nickthelegend/cell-4b/out/stl/cartridge_null.stl

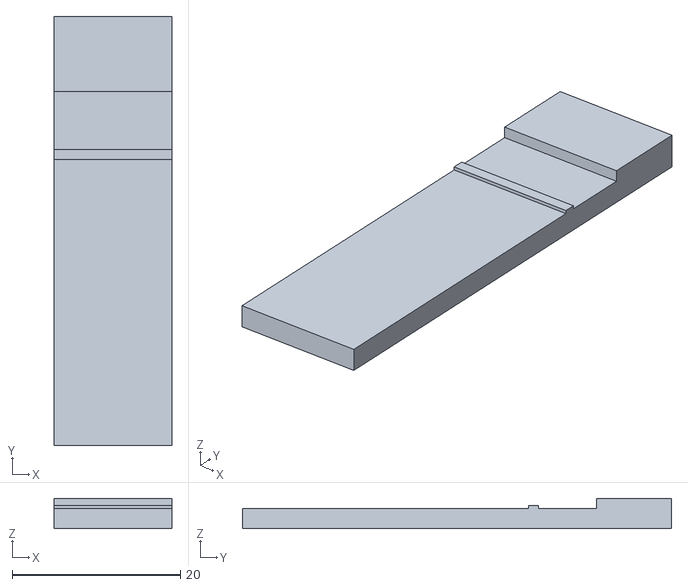
[picture p15: CAD file, 2026-08-31]
out/stl/cartridge_null.stl
14.0 x 51.0 x 3.60
