nickthelegend/cell-4b/out/stl/aperture_tube.stl

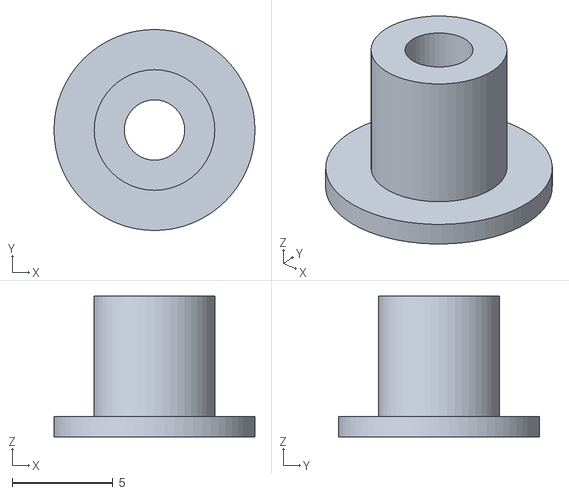
[picture p16: CAD file, 2026-08-31]
out/stl/aperture_tube.stl
10.0 x 10.0 x 7.00
