nickthelegend/cell-4b/out/stl/window_jig.stl

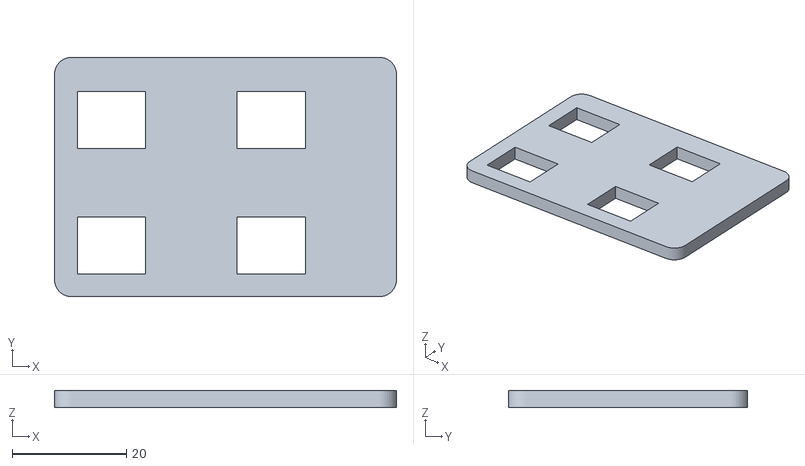
[picture p18: CAD file, 2026-08-31]
out/stl/window_jig.stl
60.0 x 42.0 x 3.00
