nickthelegend/cell-4b/out/stl/cartridge.stl

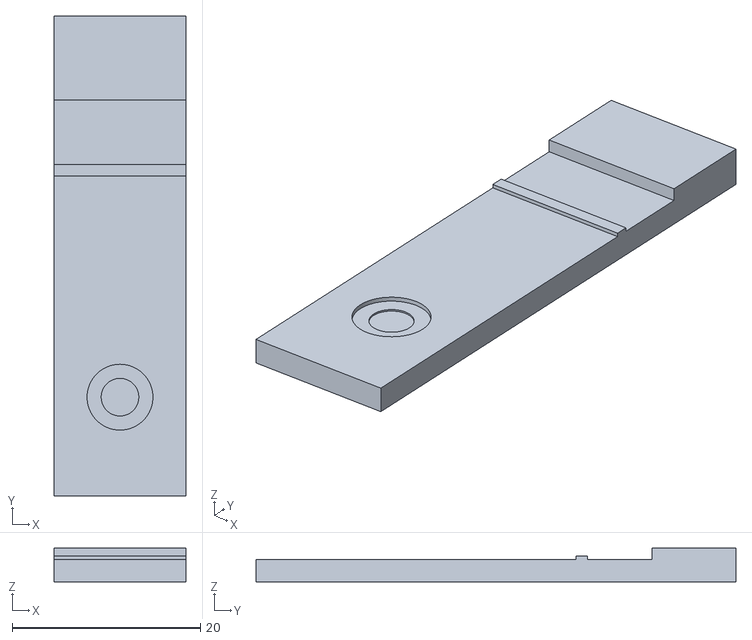
[picture p19: CAD file, 2026-08-31]
out/stl/cartridge.stl
14.0 x 51.0 x 3.60
