nickthelegend/cell-4b/videos/cell4b-assembly/snapshots/contact-sheet.jpg

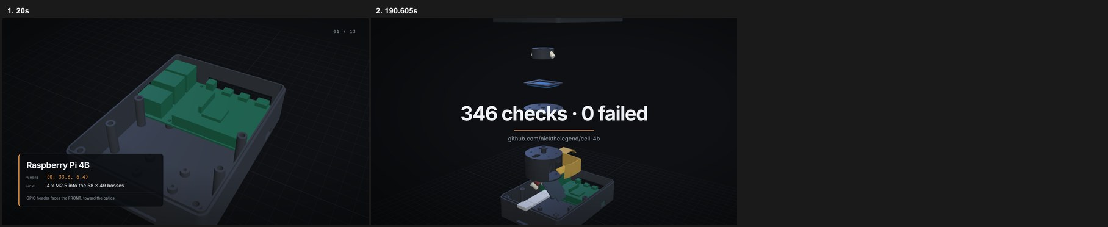
videos/cell4b-assembly/snapshots/contact-sheet.jpg
