nickthelegend/cell-4b/videos/cell4b-assembly/snapshots/frame-00-at-20s.png

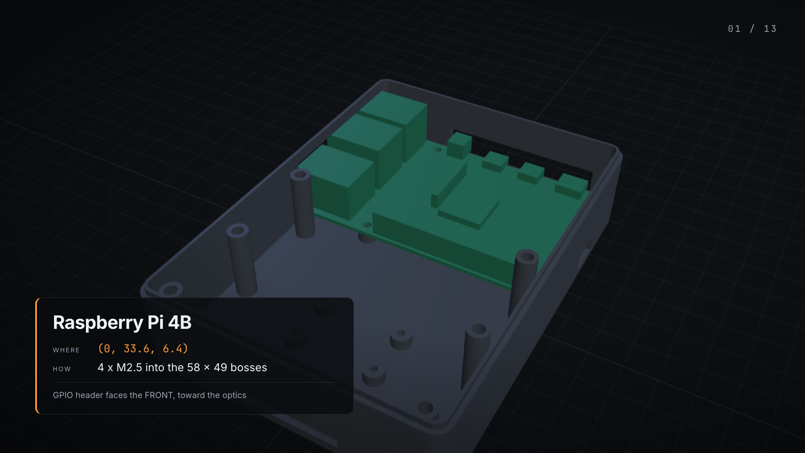
videos/cell4b-assembly/snapshots/frame-00-at-20s.png
