nickthelegend/cell-4b/videos/cell4b-assembly/snapshots/frame-01-at-190.605s.png

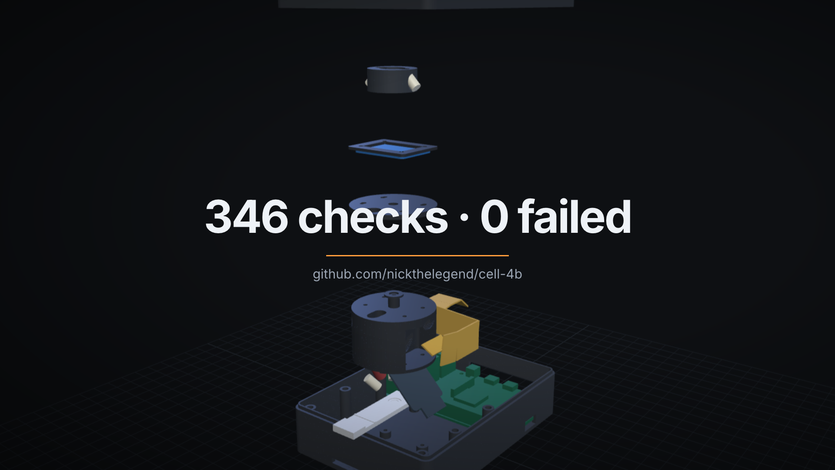
videos/cell4b-assembly/snapshots/frame-01-at-190.605s.png
