nickthelegend/cell-4b/firmware/cell4b/spectro.py

"""AS7341 spectrometer, wrapped for a 28 mm standoff.

The wrapping is the point. ASSEMBLY.md section 6 says raise ATIME/ASTEP before
M2 because this sensor sits at SENSOR_STANDOFF = 28 mm rather than upstream's
9 mm. Irradiance falls with the square of that distance, so the same integration
that lands mid-scale upstream lands near the ADC floor here -- roughly (28/9)^2
= 9.7x less light. Every default in this file is chosen for that, and
`headroom()` exists so you can prove it on a white card instead of trusting it.

Channels are F1..F8 (415, 445, 480, 515, 555, 590, 630, 680 nm) plus Clear and
NIR. 415 nm is the one M5 turns on: it is where haemoglobin absorbs and red
food dye does not.
"""
from __future__ import annotations

import statistics
import time
from dataclasses import dataclass, field

import board
import busio
from adafruit_as7341 import AS7341

I2C_ADDR = 0x39

# 415 nm first, because it is the channel the whole instrument exists to read.
BANDS = (415, 445, 480, 515, 555, 590, 630, 680)

ENABLE = 0x80          # bit 0 PON, bit 1 SP_EN

# 16-bit ADC. Above this we call it saturated and refuse to trust the number.
FULL_SCALE = 65535
SATURATED = 0.95 * FULL_SCALE
# Below this a channel is in the noise and any ratio built on it is fiction.
FLOOR = 0.02 * FULL_SCALE

# The Adafruit driver's `gain` is an ENUM INDEX, not a multiplier -- setting it
# to 8 selects index 8, which is 128x. That silently ran this file at 16x the
# intended gain until an out-of-range value (64) finally raised. Everything
# here speaks in multipliers and converts at the boundary.
# What is actually soldered on the emitters. 120 was the first build; 220 is
# what the parts drawer had. Either is fine -- both sit under the 16 mA pin
# rating, and the only thing that changes is how long the sensor stays open.
EMITTER_OHMS = 220

# The reference point the timing is scaled from: 120 ohm wanted ATIME 99 at
# ASTEP 1799, which is ~500 ms.
_REF_OHMS, _REF_ATIME = 120, 99


def atime_for(ohms: int, astep: int = 1799) -> int:
    """ATIME that holds the collected light constant as the resistor changes.

    Current goes as 1/R, so the sensor has to stay open in proportion to R.
    Clamped to the register's 255, which 220 ohm is nowhere near -- it lands
    on 182, about 916 ms, under 2% of the 46.6 s the part can integrate for.
    """
    scaled = round((_REF_ATIME + 1) * ohms / _REF_OHMS) - 1
    return max(0, min(255, scaled))


GAIN_STEPS = {0.5: 0, 1: 1, 2: 2, 4: 3, 8: 4, 16: 5, 32: 6,
              64: 7, 128: 8, 256: 9, 512: 10}


@dataclass
class Reading:
    """One set of channels, with the gain and timing that produced it."""
    channels: dict[int, int]
    clear: int
    nir: int
    atime: int
    astep: int
    gain: int
    t: float = field(default_factory=time.time)

    @property
    def integration_ms(self) -> float:
        """(ATIME+1) * (ASTEP+1) * 2.78 us, per the AS7341 datasheet."""
        return (self.atime + 1) * (self.astep + 1) * 2.78 / 1000.0

    def saturated(self) -> list[int]:
        return [b for b, v in self.channels.items() if v >= SATURATED]

    def on_floor(self) -> list[int]:
        return [b for b, v in self.channels.items() if v <= FLOOR]


class Spectrometer:
    """The AS7341 at 0x39, with defaults for a 28 mm standoff."""

    # Integration is long, deliberately, for two reasons that stack.
    #
    #   1. The sensor is at 28 mm, not upstream's 9 mm -- about 9.7x less light.
    #   2. The emitters run well under the design current. Sinking (no 2N7000
    #      since d514af1) the pin carries the LED, and a Pi pin is rated 16 mA,
    #      so the 68/47 the optical design asks for cannot be used here at all
    #      -- they would be 27.9 and 41.5 mA.
    #
    # ATIME is DERIVED from the resistor rather than hard-coded, because the
    # two have to move together: halving the drive current halves the light,
    # and the sensor has to sit open twice as long to collect the same photons.
    # Set EMITTER_OHMS to what is actually soldered and the timing follows.
    # Getting this backwards is the failure it prevents -- 220 ohm timing on
    # 120 ohm hardware over-integrates 1.8x and saturates.
    #
    # Same photons either way, so shot-noise-limited SNR is unchanged; what a
    # bigger resistor costs is read TIME, and this instrument has 46.6 s of it.
    def __init__(self, atime: int | None = None, astep: int = 1799,
                 gain: int = 8):
        if atime is None:
            atime = atime_for(EMITTER_OHMS, astep)
        self.i2c = busio.I2C(board.SCL, board.SDA)
        self.dev = AS7341(self.i2c, address=I2C_ADDR)
        self.wake()
        self.set_timing(atime, astep, gain)

    def wake(self) -> None:
        """Force PON and SP_EN, rather than trusting the power-on state.

        The Adafruit driver assumes it is talking to a freshly powered chip.
        It is not always: after a brownout the AS7341 still ACKs at 0x39 and
        every register reads back plausibly, but the ADC never converts and
        all ten channels return a hard zero. That is indistinguishable from a
        dark chamber, which is exactly the reading this device has to trust,
        so it gets forced on every construction instead of being diagnosed
        again. 0x80 is ENABLE: bit 0 PON, bit 1 SP_EN.
        """
        for value in (0x00, 0x01, 0x03):
            self._poke(ENABLE, value)
            time.sleep(0.01)
        got = self._peek(ENABLE)
        if got & 0x03 != 0x03:
            raise RuntimeError(
                f"AS7341 ENABLE reads 0x{got:02x} after being set to 0x03 -- "
                "the chip answers on I2C but will not turn its ADC on")

    def _poke(self, reg: int, value: int) -> None:
        while not self.i2c.try_lock():
            pass
        try:
            self.i2c.writeto(I2C_ADDR, bytes((reg, value)))
        finally:
            self.i2c.unlock()

    def _peek(self, reg: int) -> int:
        buf = bytearray(1)
        while not self.i2c.try_lock():
            pass
        try:
            self.i2c.writeto_then_readfrom(I2C_ADDR, bytes((reg,)), buf)
        finally:
            self.i2c.unlock()
        return buf[0]

    def set_timing(self, atime: int, astep: int, gain: float) -> None:
        if gain not in GAIN_STEPS:
            raise ValueError(
                f"gain must be one of {sorted(GAIN_STEPS)} (a multiplier, "
                f"not the register index) -- got {gain}")
        self.atime, self.astep, self.gain = atime, astep, gain
        self.dev.atime = atime
        self.dev.astep = astep
        self.dev.gain = GAIN_STEPS[gain]
        # One integration plus slack, so the first read after a change is not
        # a leftover from the old timing.
        self._wait = ((atime + 1) * (astep + 1) * 2.78 / 1e6) + 0.05

    def read(self) -> Reading:
        time.sleep(self._wait)
        ch = self.dev.all_channels          # F1..F8 in order
        return Reading(channels=dict(zip(BANDS, ch)),
                       clear=self.dev.channel_clear,
                       nir=self.dev.channel_nir,
                       atime=self.atime, astep=self.astep, gain=self.gain)

    def average(self, n: int = 10) -> tuple[Reading, dict[int, float]]:
        """n reads averaged, plus per-band relative standard deviation in %.

        RSD is what M2 is stated in ("< 1 % RSD over 100 reads"), so it is
        returned rather than left for the caller to recompute.
        """
        runs = [self.read() for _ in range(n)]
        mean = {b: int(statistics.fmean(r.channels[b] for r in runs))
                for b in BANDS}
        rsd = {}
        for b in BANDS:
            vals = [r.channels[b] for r in runs]
            m = statistics.fmean(vals)
            rsd[b] = (statistics.stdev(vals) / m * 100.0) if m and n > 1 else 0.0
        last = runs[-1]
        avg = Reading(channels=mean,
                      clear=int(statistics.fmean(r.clear for r in runs)),
                      nir=int(statistics.fmean(r.nir for r in runs)),
                      atime=last.atime, astep=last.astep, gain=last.gain)
        return avg, rsd

    def headroom(self, r: Reading) -> dict[int, float]:
        """Each band as a percentage of full scale.

        ASSEMBLY.md section 6: confirm 415 nm is comfortably off the floor on a
        white card, and if it is not, say so in the writeup -- that is a
        result, not a bug to hide.
        """
        return {b: v / FULL_SCALE * 100.0 for b, v in r.channels.items()}

    def close(self) -> None:
        try:
            self.i2c.deinit()
        except Exception:
            pass

    def __enter__(self) -> "Spectrometer":
        return self

    def __exit__(self, *exc) -> None:
        self.close()
