nickthelegend/cell-4b/firmware/cell4b/selftest.py

"""Bring-up checks, in the order that isolates faults fastest.

Each check assumes the ones before it passed, so the first failure is the one
worth acting on. That ordering matters more than it sounds: a light leak and a
dead LED both show up as "415 nm reads nothing", and telling them apart after
the fact costs an hour.

These are bench checks for a build you just wired. The milestones they feed
(M2, M4, M5) are upstream BUILD.md section 15, and this file deliberately stops
short of M5 -- that one needs blood, consent and SAFETY.md, not a script.
"""
from __future__ import annotations

import os
import shutil
import subprocess
import time

from .hw import Bench, InterlockError
from .spectro import FLOOR, FULL_SCALE, Spectrometer

PASS, FAIL, WARN = "PASS", "FAIL", "WARN"

# Debian keeps i2cdetect in /usr/sbin, which is NOT on a normal user's PATH --
# so a bare subprocess call for it raises FileNotFoundError on a stock Pi OS
# and reads like i2c-tools is missing when it is installed and working.
I2CDETECT = shutil.which("i2cdetect") or "/usr/sbin/i2cdetect"


def _line(tag, name, detail=""):
    print(f"  [{tag:4s}] {name}" + (f" -- {detail}" if detail else ""))
    return tag


def check_i2c() -> str:
    """Both devices answer. 0x39 is the AS7341; 0x3C/0x3D is the OLED."""
    try:
        out = subprocess.run([I2CDETECT, "-y", "1"], capture_output=True,
                             text=True, timeout=10).stdout
    except FileNotFoundError:
        return _line(FAIL, "I2C bus", "i2c-tools not installed "
                     "(sudo apt install i2c-tools)")
    except Exception as e:
        return _line(FAIL, "I2C bus", f"i2cdetect failed: {e}")
    if not os.path.exists("/dev/i2c-1"):
        return _line(FAIL, "I2C bus", "/dev/i2c-1 does not exist -- the bus is "
                     "not enabled. sudo raspi-config nonint do_i2c 0, "
                     "then reboot.")
    found = "39" in out
    oled = ("3c" in out) or ("3d" in out)
    if not found:
        return _line(FAIL, "AS7341 at 0x39", "not on the bus -- check SDA/SCL, "
                     "3V3, and that raspi-config enabled I2C")
    _line(PASS, "AS7341 at 0x39")
    _line(PASS if oled else WARN, "OLED at 0x3C/0x3D",
          "" if oled else "absent; measurements still work")
    return PASS


def check_interlock() -> str:
    """The laser must refuse to fire with the slot empty.

    Tested by asking it to, with no cartridge in, and requiring the refusal.
    A pass here means the SOFTWARE interlock works; it says nothing about the
    hardware one through the microswitch, which you verify with a meter.
    """
    from .hw import LASER_FITTED
    if not LASER_FITTED:
        return _line(WARN, "laser interlock",
                     "no laser driver fitted -- nothing to interlock yet. "
                     "M2-M5 do not need it; M6 speckle does.")
    with Bench() as b:
        if b.seated:
            return _line(WARN, "laser interlock",
                         "a cartridge is seated -- remove it and re-run to "
                         "actually test the refusal")
        try:
            with b.laser():
                pass
        except InterlockError:
            return _line(PASS, "laser interlock", "refused with slot empty")
        return _line(FAIL, "laser interlock",
                     "LASER FIRED WITH NO CARTRIDGE. Stop and fix GPIO22 "
                     "before anything else.")


def check_cartridge_switch() -> str:
    """GPIO22 must change state when you seat a cartridge."""
    with Bench() as b:
        empty = b.seated
        input("  seat a cartridge, then press Enter... ")
        seated = b.seated
        if empty == seated:
            return _line(FAIL, "cartridge switch",
                         f"GPIO22 did not change (still {'LOW' if seated else 'HIGH'})")
        if not seated:
            return _line(FAIL, "cartridge switch",
                         "reads HIGH when seated -- switch is wired inverted")
        return _line(PASS, "cartridge switch", "LOW when seated")


def check_emitters() -> str:
    """Each emitter must raise Clear above dark.

    NEEDS A CARTRIDGE SEATED. The emitters point down at the read spot, not at
    the sensor -- the AS7341 only ever sees light that something SCATTERS back
    up the aperture. With the slot empty there is nothing to scatter off and
    the light leaves through the slot, so a perfectly good LED reads as dark.
    This check used to run without one and blamed the wiring for it.
    """
    with Bench() as b, Spectrometer() as s:
        if not b.seated:
            return _line(WARN, "emitters",
                         "no cartridge seated -- nothing for the light to "
                         "scatter off. Seat the reference cartridge and re-run; "
                         "an empty chamber reads dark no matter how good the LED.")
        with b.dark():
            dark = s.read().clear
        rows, bad = [], []
        for name, cm in (("white", b.white), ("940 nm IR", b.infrared)):
            with cm():
                lit = s.read().clear
            gain = lit - dark
            rows.append(f"{name} +{gain}")
            if gain < 200:
                bad.append(name)
        detail = ", ".join(rows) + f" (dark {dark})"
        if bad:
            from .hw import EMITTER_SINK
            hint = ("polarity (sink build: LOW is lit), the resistor, and "
                    "which rail it went to" if EMITTER_SINK else
                    "the FET, the resistor, and which rail it went to")
            return _line(FAIL, "emitters", detail +
                         f" -- no response from {', '.join(bad)}: check " + hint)
        return _line(PASS, "emitters", detail)


def check_headroom(n: int = 20) -> str:
    """M2's precondition: 415 nm comfortably off the floor on a white card.

    At SENSOR_STANDOFF = 28 mm this is the check most likely to fail, and
    ASSEMBLY.md is explicit that a failure here is a result to report rather
    than a defect to bury.
    """
    with Bench() as b, Spectrometer() as s:
        with b.white():
            avg, rsd = s.average(n)
        pct = avg.channels[415] / FULL_SCALE * 100.0
        detail = f"415 nm at {pct:.1f}% of full scale, RSD {rsd[415]:.2f}% over {n}"
        if avg.channels[415] <= FLOOR:
            return _line(FAIL, "415 nm headroom", detail +
                         " -- on the ADC floor. Raise ATIME/ASTEP or gain, and "
                         "if it will not lift, SAY SO in the writeup")
        if pct < 10:
            return _line(WARN, "415 nm headroom", detail + " -- thin but usable")
        return _line(PASS, "415 nm headroom", detail)


def check_light_tight(n: int = 10) -> str:
    """M4: Clear under 0.5% of full scale with the chamber shut and lit."""
    print("  put the case under the brightest light you have, lid ON.")
    input("  press Enter when it is... ")
    with Bench() as b, Spectrometer() as s:
        with b.dark():
            avg, _ = s.average(n)
    pct = avg.clear / FULL_SCALE * 100.0
    detail = f"Clear at {pct:.3f}% of full scale"
    if pct >= 0.5:
        return _line(FAIL, "light-tight (M4)", detail +
                     " -- over 0.5%. Paint the bores matte black, check the "
                     "slot baffle and the lap joint")
    return _line(PASS, "light-tight (M4)", detail)


# Checks that only mean anything once the optical head is built. On a
# breadboard the emitters are not in their bores aiming at a read spot and the
# sensor is not looking down the aperture, so "no light" says nothing about the
# wiring -- it says the optics do not exist yet. Reporting that as FAIL sent us
# hunting a wiring fault that was never there.
NEEDS_OPTICS = {"emitters", "headroom", "lighttight"}


def check_pulse():
    """The touch tier's sensor, and whether a finger is on it.

    Interactive because it cannot be otherwise: the measurement IS a finger.
    Without one the honest answer is that the sensor is present and idle, not
    that the gate failed.
    """
    try:
        from cell4b.pulse import Max3010x, analyse, NoSensor, PERFUSION_MAX
    except Exception as e:
        return _line(FAIL, "pulse sensor", f"cannot import: {type(e).__name__}")
    try:
        dev = Max3010x()
    except NoSensor as e:
        return _line(FAIL, "pulse sensor", str(e))
    except Exception as e:
        return _line(FAIL, "pulse sensor", f"{type(e).__name__}: {e}")

    print(f"      MAX3010x found, part id 0x{dev.part_id:02x}")
    print("      put a finger on the ring and hold still -- 10 s")
    dev.configure()
    time.sleep(0.3)
    _red, ir = dev.collect(10.0)
    p = analyse(ir)
    if p.present:
        return _line(PASS, "pulse sensor",
                     f"{p.bpm:.0f} bpm, confidence {p.confidence:.2f}, "
                     f"perfusion {p.perfusion:.2f}%")
    return _line(WARN, "pulse sensor",
                 f"no pulse -- {p.reason or 'nothing detected'} "
                 f"(bpm {p.bpm:.0f}, conf {p.confidence:.2f}, "
                 f"perf {p.perfusion:.2f}%)")


ORDER = [
    ("i2c", check_i2c, False),
    ("interlock", check_interlock, False),
    ("switch", check_cartridge_switch, True),
    ("emitters", check_emitters, False),
    ("headroom", check_headroom, False),
    ("lighttight", check_light_tight, True),
    ("pulse", check_pulse, True),
]


def main(only: str | None = None, skip_prompts: bool = False,
         breadboard: bool = False) -> int:
    print("CELL-4B self-test" + (" -- breadboard stage\n" if breadboard else "\n"))
    results = {}
    for name, fn, interactive in ORDER:
        if only and name != only:
            continue
        if breadboard and name in NEEDS_OPTICS:
            _line(WARN, name, "needs the assembled head -- skipped on a breadboard")
            continue
        if interactive and skip_prompts:
            _line(WARN, name, "skipped (needs you at the bench)")
            continue
        try:
            results[name] = fn()
        except Exception as e:
            results[name] = _line(FAIL, name, f"{type(e).__name__}: {e}")
        if results.get(name) == FAIL:
            print("\n  stopping at the first failure -- later checks assume "
                  "this one passed.")
            break
    bad = sum(1 for v in results.values() if v == FAIL)
    print(f"\n{len(results)} checks, {bad} failed")
    return 1 if bad else 0
